brain-zhang/icaplamp/doc/image/msp430.jpg

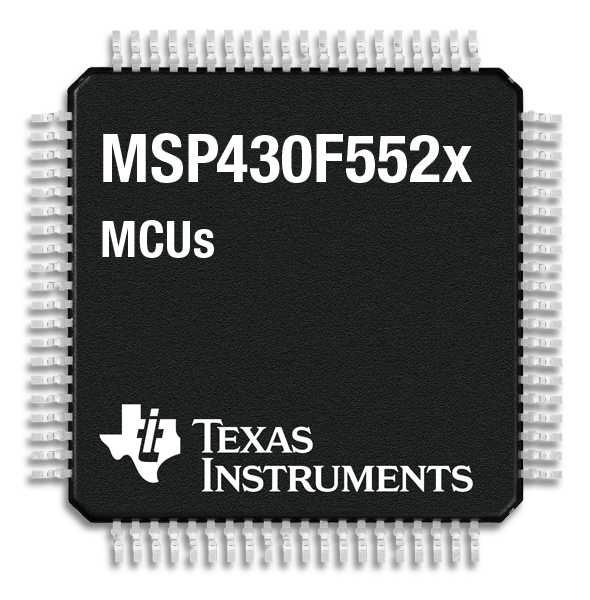
doc/image/msp430.jpg
